xoseperez/sonometer/model/sonometer-wood-4mm.png

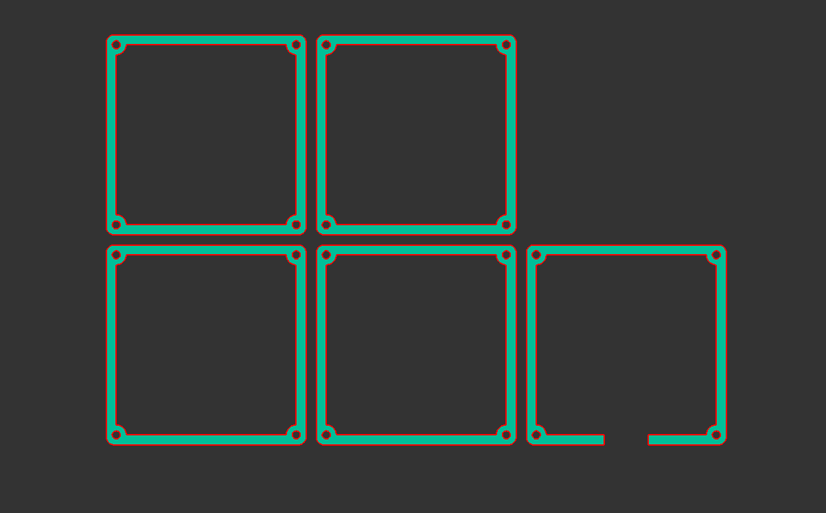
model/sonometer-wood-4mm.png
